Professor-plum/BSides-SLC-Badge-2020/resources/Chess_clean.jpg

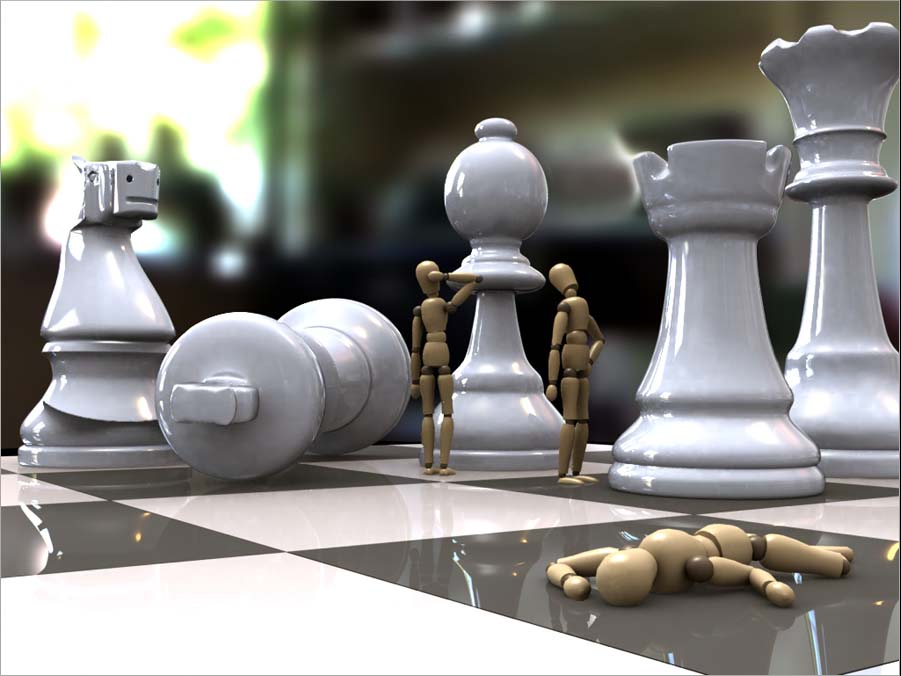
resources/Chess_clean.jpg
