Professor-plum/BSides-SLC-Badge-2020/source/BsidesSLC2020/Core/Inc/bsides_logo.h

/*
 * bsides_logo.h
 *
 *  Created on: Nov 3, 2019
 *      Author: plum
 */

#ifndef INC_BSIDES_LOGO_H_
#define INC_BSIDES_LOGO_H_

#define bsides_width 104
#define bsides_height 144
static const char bsides_bits[] = {
  0x00, 0x00, 0x00, 0x00, 0x00, 0x80, 0xFF, 0x01, 0x00, 0x00, 0x00, 0x00,
  0x00, 0x00, 0x00, 0x00, 0x00, 0x00, 0xFC, 0xFF, 0x3F, 0x00, 0x00, 0x00,
  0x00, 0x00, 0x00, 0x00, 0x00, 0x00, 0xC0, 0xFF, 0xFF, 0xFF, 0x03, 0x00,
  0x00, 0x00, 0x00, 0x00, 0x00, 0x00, 0x00, 0xF8, 0xFF, 0xFF, 0xFF, 0x1F,
  0x00, 0x00, 0x00, 0x00, 0x00, 0x00, 0x00, 0x00, 0xFF, 0xFF, 0xE7, 0xFF,
  0xFF, 0x00, 0x00, 0x00, 0x00, 0x00, 0x00, 0x00, 0xC0, 0xFF, 0x07, 0x00,
  0xE0, 0xFF, 0x03, 0x00, 0x00, 0x00, 0x00, 0x00, 0x00, 0xF0, 0x7F, 0x00,
  0x00, 0x00, 0xFE, 0x0F, 0x00, 0x00, 0x00, 0x00, 0x00, 0x00, 0xFC, 0x0F,
  0x00, 0x00, 0x00, 0xF0, 0x3F, 0x00, 0x00, 0x00, 0x00, 0x00, 0x00, 0xFE,
  0x03, 0x00, 0x00, 0x00, 0xC0, 0x7F, 0x00, 0x00, 0x00, 0x00, 0x00, 0x80,
  0xFF, 0x00, 0x00, 0x00, 0x00, 0x00, 0xFF, 0x01, 0x00, 0x00, 0x00, 0x00,
  0xC0, 0x3F, 0x00, 0x00, 0x00, 0x00, 0x00, 0xFC, 0x03, 0x00, 0x00, 0x00,
  0x00, 0xF0, 0x0F, 0x00, 0x00, 0x00, 0x00, 0x00, 0xF0, 0x0F, 0x00, 0x00,
  0x00, 0x00, 0xF8, 0x03, 0x00, 0x00, 0x00, 0x00, 0x00, 0xC0, 0x1F, 0x00,
  0x00, 0x00, 0x00, 0xFC, 0x01, 0x00, 0x00, 0x00, 0x00, 0x00, 0x80, 0x3F,
  0x00, 0x00, 0x00, 0x00, 0xFE, 0x00, 0x00, 0x00, 0x00, 0x00, 0x00, 0x00,
  0x7F, 0x00, 0x00, 0x00, 0x00, 0x3F, 0x00, 0x00, 0x00, 0x00, 0x00, 0x00,
  0x00, 0xFC, 0x00, 0x00, 0x00, 0x80, 0x1F, 0x00, 0x00, 0x00, 0x00, 0x00,
  0x00, 0x00, 0xF8, 0x01, 0x00, 0x00, 0xC0, 0x0F, 0x00, 0x00, 0x00, 0x00,
  0x00, 0x00, 0x00, 0xF0, 0x03, 0x00, 0x00, 0xE0, 0x07, 0x00, 0x00, 0x00,
  0x00, 0x00, 0x00, 0x00, 0xE0, 0x07, 0x00, 0x00, 0xF0, 0x03, 0x00, 0x00,
  0x00, 0x00, 0x03, 0x00, 0x00, 0xC0, 0x0F, 0x00, 0x00, 0xF0, 0x01, 0x00,
  0x00, 0x00, 0x80, 0x07, 0x00, 0x00, 0x80, 0x0F, 0x00, 0x00, 0xF8, 0x00,
  0x00, 0x00, 0x00, 0x80, 0x07, 0x00, 0x00, 0x00, 0x1F, 0x00, 0x00, 0x7C,
  0x00, 0x00, 0x00, 0x00, 0x80, 0x07, 0x00, 0x00, 0x00, 0x3E, 0x00, 0x00,
  0x7E, 0x00, 0x00, 0x00, 0x00, 0x80, 0x07, 0x00, 0x00, 0x00, 0x7E, 0x00,
  0x00, 0x3E, 0x00, 0x00, 0x00, 0x00, 0x80, 0x0F, 0x00, 0x00, 0x00, 0x7C,
  0x00, 0x00, 0x1F, 0x00, 0x00, 0x00, 0x00, 0x80, 0x0F, 0x00, 0x00, 0x00,
  0xF8, 0x00, 0x00, 0x1F, 0x00, 0x00, 0x00, 0x00, 0xC0, 0x0F, 0x00, 0x00,
  0x00, 0xF8, 0x00, 0x80, 0x0F, 0x00, 0x00, 0x00, 0x00, 0xC0, 0x1F, 0x00,
  0x00, 0x00, 0xF0, 0x01, 0x80, 0x0F, 0x00, 0x00, 0x00, 0x00, 0xC0, 0x1D,
  0x00, 0x00, 0x00, 0xF0, 0x01, 0xC0, 0x07, 0x00, 0x00, 0x00, 0x00, 0xC0,
  0x1D, 0x00, 0x00, 0x00, 0xE0, 0x03, 0xC0, 0x03, 0x00, 0x00, 0x00, 0x00,
  0xC0, 0x1D, 0x00, 0x00, 0x00, 0xC0, 0x03, 0xE0, 0x03, 0x00, 0x00, 0x00,
  0x00, 0xC0, 0x39, 0x00, 0x00, 0x00, 0xC0, 0x07, 0xE0, 0x01, 0x00, 0x00,
  0x00, 0x00, 0xE0, 0x39, 0x00, 0x00, 0x00, 0x80, 0x07, 0xF0, 0x01, 0x00,
  0x00, 0x00, 0x00, 0xE0, 0x38, 0x00, 0x00, 0x00, 0x80, 0x0F, 0xF0, 0x01,
  0x00, 0x00, 0x00, 0x00, 0xE0, 0x78, 0x00, 0x00, 0x00, 0x80, 0x0F, 0xF0,
  0x00, 0x00, 0x00, 0x00, 0x00, 0xE0, 0x70, 0x00, 0x00, 0x00, 0x00, 0x0F,
  0xF8, 0x00, 0x00, 0x00, 0x00, 0x00, 0xE0, 0x70, 0x00, 0x00, 0x00, 0x00,
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
  };


#endif /* INC_BSIDES_LOGO_H_ */
