Professor-plum/BSides-SLC-Badge-2020/source/BsidesSLC2020/Core/Inc/fakeDisk.h

#ifndef FAKE_DISK
#define FAKE_DISK

const uint8_t fake_mbr[] = {
		0xeb, 0x3c, 0x90,
		'P', 'l', 'u', 'm', ' ', 'F', 'S', 0,
		0x00, 0x02,
		0x04,
		0x01, 0x00,
		0x02,
		0x70, 0x00,
		0x00, 0x08, // 0x00, 0x08  Small Sectors 0x800 == 2048
		0xf8,
		0x02, 0x00, // 0x02, 0x00  Sector per FAT
		0x20, 0x00,
		0x40, 0x00,
		0x00, 0x00, 0x00, 0x00,
		0x00, 0x00, 0x00, 0x00,
		0x80,
		0x00,
		0x29,
		'P','L','U','M',
		'C', 'A', 'S', 'E', ' ', 'F', 'I', 'L', 'E', ' ', ' ',
		'F', 'A', 'T', '1', '2', ' ', ' ', ' '
};

const uint8_t fake_fat[] = {
		0xF8, 0xFF, 0xFF, 0x00, 0x40, 0x00, 0x05, 0x60, 0x00, 0x07, 0x80, 0x00, 0x09, 0xA0, 0x00, 0x0B,
		0xC0, 0x00, 0x0D, 0xE0, 0x00, 0x0F, 0x00, 0x01, 0x11, 0x20, 0x01, 0x13, 0x40, 0x01, 0xFF, 0x6F,
		0x01, 0x17, 0x80, 0x01, 0x19, 0xA0, 0x01, 0x1B, 0xC0, 0x01, 0x1D, 0xE0, 0x01, 0x1F, 0x00, 0x02,
		0x21, 0x20, 0x02, 0x23, 0x40, 0x02, 0xFF, 0x6F, 0x02, 0x27, 0x80, 0x02, 0x29, 0xA0, 0x02, 0x2B,
		0xC0, 0x02, 0x2D, 0xE0, 0x02, 0x2F, 0x00, 0x03, 0x31, 0x20, 0x03, 0x33, 0x40, 0x03, 0x35, 0x60,
		0x03, 0x37, 0x80, 0x03, 0x39, 0xA0, 0x03, 0x3B, 0xC0, 0x03, 0x3D, 0xE0, 0x03, 0x3F, 0x00, 0x04,
		0x41, 0xF0, 0xFF, 0x43, 0x40, 0x04, 0x45, 0x60, 0x04, 0x47, 0x80, 0x04, 0x49, 0xA0, 0x04, 0x4B,
		0xC0, 0x04, 0x4D, 0xE0, 0x04, 0x4F, 0x00, 0x05, 0x51, 0x20, 0x05, 0x53, 0xF0, 0xFF, 0x00, 0x00
};
//const uint8_t fake_fat[] = {0xf8, 0xff, 0xff, 0x00, 0xf0, 0xff, 0x05, 0x60, 0x00, 0x07, 0xf0, 0xff, 0xff, 0x0f};
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
