Professor-plum/BSides-SLC-Badge-2020/source/BsidesSLC2020/Core/Inc/custom_bus.h

/**
  ******************************************************************************
  * @file           : custom_bus.h
  * @brief          : header file for the BSP BUS IO driver
  ******************************************************************************
  * @attention
  *
  * <h2><center>&copy; Copyright (c) 2020 STMicroelectronics.
  * All rights reserved.</center></h2>
  *
  * This software component is licensed by ST under Ultimate Liberty license
  * SLA0044, the "License"; You may not use this file except in compliance with
  * the License. You may obtain a copy of the License at:
  *                             www.st.com/SLA0044
  *
  ******************************************************************************
*/

/* Define to prevent recursive inclusion -------------------------------------*/
#ifndef CUSTOM_BUS_H
#define CUSTOM_BUS_H

#ifdef __cplusplus
 extern "C" {
#endif

/* Includes ------------------------------------------------------------------*/
#include "custom_conf.h"
#include "custom_errno.h"

/** @addtogroup BSP
  * @{
  */

/** @addtogroup CUSTOM
  * @{
  */

/** @defgroup CUSTOM_BUS CUSTOM BUS
  * @{
  */

/** @defgroup CUSTOM_BUS_Exported_Constants CUSTOM BUS Exported Constants
  * @{
  */

#define BUS_I2C1_INSTANCE I2C1
#define BUS_I2C1_SCL_GPIO_PIN GPIO_PIN_6
#define BUS_I2C1_SCL_GPIO_AF GPIO_AF1_I2C1
#define BUS_I2C1_SCL_GPIO_CLK_ENABLE() __HAL_RCC_GPIOB_CLK_ENABLE()
#define BUS_I2C1_SCL_GPIO_PORT GPIOB
#define BUS_I2C1_SCL_GPIO_CLK_DISABLE() __HAL_RCC_GPIOB_CLK_DISABLE()
#define BUS_I2C1_SDA_GPIO_PIN GPIO_PIN_7
#define BUS_I2C1_SDA_GPIO_AF GPIO_AF1_I2C1
#define BUS_I2C1_SDA_GPIO_CLK_ENABLE() __HAL_RCC_GPIOB_CLK_ENABLE()
#define BUS_I2C1_SDA_GPIO_PORT GPIOB
#define BUS_I2C1_SDA_GPIO_CLK_DISABLE() __HAL_RCC_GPIOB_CLK_DISABLE()
#ifndef BUS_I2C1_POLL_TIMEOUT
   #define BUS_I2C1_POLL_TIMEOUT                0x1000U   
#endif
/* I2C1 Frequeny in Hz  */
#ifndef BUS_I2C1_FREQUENCY  
   #define BUS_I2C1_FREQUENCY  1000000U /* Frequency of I2Cn = 100 KHz*/
#endif

/**
  * @}
  */

/** @defgroup CUSTOM_BUS_Private_Types CUSTOM BUS Private types
  * @{
  */
#if (USE_HAL_I2C_REGISTER_CALLBACKS == 1)
typedef struct
{
  pI2C_CallbackTypeDef  pMspInitCb;
  pI2C_CallbackTypeDef  pMspDeInitCb;
}BSP_I2C_Cb_t;
#endif /* (USE_HAL_I2C_REGISTER_CALLBACKS == 1) */
/**
  * @}
  */
  
/** @defgroup CUSTOM_LOW_LEVEL_Exported_Variables LOW LEVEL Exported Constants
  * @{
  */

extern I2C_HandleTypeDef hi2c1;

/**
  * @}
  */

/** @addtogroup CUSTOM_BUS_Exported_Functions
  * @{
  */    

/* BUS IO driver over I2C Peripheral */
HAL_StatusTypeDef MX_I2C1_Init(I2C_HandleTypeDef* hi2c);
int32_t BSP_I2C1_Init(void);
int32_t BSP_I2C1_DeInit(void);
int32_t BSP_I2C1_IsReady(uint16_t DevAddr, uint32_t Trials);
int32_t BSP_I2C1_WriteReg(uint16_t Addr, uint16_t Reg, uint8_t *pData, uint16_t Length);
int32_t BSP_I2C1_ReadReg(uint16_t Addr, uint16_t Reg, uint8_t *pData, uint16_t Length);
int32_t BSP_I2C1_WriteReg16(uint16_t Addr, uint16_t Reg, uint8_t *pData, uint16_t Length);
int32_t BSP_I2C1_ReadReg16(uint16_t Addr, uint16_t Reg, uint8_t *pData, uint16_t Length);
int32_t BSP_I2C1_Send(uint16_t DevAddr, uint8_t *pData, uint16_t Length);
int32_t BSP_I2C1_Recv(uint16_t DevAddr, uint8_t *pData, uint16_t Length);
int32_t BSP_I2C1_SendRecv(uint16_t DevAddr, uint8_t *pTxdata, uint8_t *pRxdata, uint16_t Length);
#if (USE_HAL_I2C_REGISTER_CALLBACKS == 1)
int32_t BSP_I2C1_RegisterDefaultMspCallbacks (void);
int32_t BSP_I2C1_RegisterMspCallbacks (BSP_I2C_Cb_t *Callbacks);
#endif /* (USE_HAL_I2C_REGISTER_CALLBACKS == 1) */

int32_t BSP_GetTick(void);

/**
  * @}
  */

/**
  * @}
  */

/**
  * @}
  */

/**
  * @}
  */
#ifdef __cplusplus
}
#endif

#endif /* CUSTOM_BUS_H */

/************************ (C) COPYRIGHT STMicroelectronics *****END OF FILE****/
