Professor-plum/BSides-SLC-Badge-2020/source/BsidesSLC2020/Core/Inc/RTE_Components.h

/**
  ******************************************************************************
  * @file    
  * @author  MCD Application Team
  * @version V2.0.0
  ******************************************************************************
  * @attention
  *
  * COPYRIGHT(c) 2020 STMicroelectronics
  *
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
  */
  /* Define to prevent recursive inclusion -------------------------------------*/
#ifndef  __RTE_COMPONENTS_H__
#define  __RTE_COMPONENTS_H__ 

/* Defines ------------------------------------------------------------------*/
/* STMicroelectronics.X-CUBE-MEMS1.6.2.0 */
#define LIS2DH12_ACC_I2C
/* STMicroelectronics.X-CUBE-NFC4.1.4.0 */
#define LIB_NDEF
#define Interface
#define ST25DV_NFC4_I2C 
 
#endif /* __RTE_COMPONENTS_H__ */
