Professor-plum/BSides-SLC-Badge-2020/source/BsidesSLC2020/Core/Inc/bigdigits.h

#ifndef BIG_DIGITS_H
#define BIG_DIGITS_H

#define BD_WIDTH	14
#define BD_HEIGHT	21

static const char bigDigits[] = {
		  0x0F, 0xC0, 0x3F, 0xF0, 0x3F, 0xF0, 0x78, 0x78, 0x70, 0x38, 0xF0, 0x38,
		  0xE0, 0x1C, 0xE0, 0x1C, 0xE0, 0x1C, 0xE0, 0x1C, 0xE0, 0x1C, 0xE0, 0x1C,
		  0xE0, 0x1C, 0xE0, 0x1C, 0xE0, 0x1C, 0xF0, 0x3C, 0x70, 0x38, 0x78, 0x78,
		  0x3F, 0xF0, 0x3F, 0xF0, 0x0F, 0xC0, 0x00, 0x60, 0x00, 0xE0, 0x01, 0xE0,
		  0x03, 0xE0, 0x07, 0xE0, 0x0E, 0xE0, 0x0C, 0xE0, 0x08, 0xE0, 0x00, 0xE0,
		  0x00, 0xE0, 0x00, 0xE0, 0x00, 0xE0, 0x00, 0xE0, 0x00, 0xE0, 0x00, 0xE0,
		  0x00, 0xE0, 0x00, 0xE0, 0x00, 0xE0, 0x00, 0xE0, 0x00, 0xE0, 0x00, 0xE0,
		  0x0F, 0xC0, 0x3F, 0xE0, 0x7F, 0xF0, 0x70, 0xF8, 0xE0, 0x78, 0xE0, 0x38,
		  0x00, 0x38, 0x00, 0x38, 0x00, 0x70, 0x00, 0x70, 0x00, 0xE0, 0x01, 0xC0,
		  0x03, 0x80, 0x07, 0x00, 0x0E, 0x00, 0x1C, 0x00, 0x38, 0x00, 0x70, 0x00,
		  0xFF, 0xF8, 0xFF, 0xF8, 0xFF, 0xF8, 0x0F, 0x80, 0x3F, 0xE0, 0x7F, 0xF0,
		  0xF0, 0x78, 0xE0, 0x38, 0x00, 0x38, 0x00, 0x38, 0x00, 0x38, 0x00, 0xF0,
		  0x07, 0xE0, 0x07, 0xF0, 0x00, 0x38, 0x00, 0x3C, 0x00, 0x1C, 0x00, 0x1C,
		  0xE0, 0x1C, 0xF0, 0x3C, 0x70, 0x78, 0x7F, 0xF8, 0x3F, 0xF0, 0x0F, 0xC0,
		  0x00, 0x30, 0x00, 0x70, 0x00, 0xF0, 0x01, 0xF0, 0x01, 0xF0, 0x03, 0xF0,
		  0x07, 0x70, 0x0E, 0x70, 0x1E, 0x70, 0x1C, 0x70, 0x38, 0x70, 0x70, 0x70,
		  0xE0, 0x70, 0xFF, 0xFC, 0xFF, 0xFC, 0xFF, 0xFC, 0x00, 0x70, 0x00, 0x70,
		  0x00, 0x70, 0x00, 0x70, 0x00, 0x70, 0x3F, 0xF8, 0x3F, 0xF8, 0x3F, 0xF8,
		  0x70, 0x00, 0x70, 0x00, 0x70, 0x00, 0x70, 0x00, 0x77, 0xC0, 0xFF, 0xF0,
		  0xFF, 0xF8, 0xF0, 0x78, 0x00, 0x3C, 0x00, 0x1C, 0x00, 0x1C, 0x00, 0x1C,
		  0xE0, 0x1C, 0xE0, 0x38, 0x70, 0x78, 0x7F, 0xF0, 0x3F, 0xE0, 0x0F, 0xC0,
		  0x07, 0xE0, 0x1F, 0xF0, 0x3F, 0xF8, 0x38, 0x3C, 0x70, 0x1C, 0x70, 0x00,
		  0xE0, 0x00, 0xE3, 0xC0, 0xEF, 0xF0, 0xFF, 0xF8, 0xF8, 0x78, 0xF0, 0x3C,
		  0xE0, 0x1C, 0xE0, 0x1C, 0xE0, 0x1C, 0xE0, 0x1C, 0x70, 0x3C, 0x78, 0x78,
		  0x3F, 0xF8, 0x1F, 0xF0, 0x07, 0xC0, 0xFF, 0xF8, 0xFF, 0xF8, 0xFF, 0xF8,
		  0x00, 0x30, 0x00, 0x70, 0x00, 0xE0, 0x00, 0xC0, 0x01, 0xC0, 0x03, 0x80,
		  0x03, 0x80, 0x07, 0x00, 0x07, 0x00, 0x07, 0x00, 0x0E, 0x00, 0x0E, 0x00,
		  0x0E, 0x00, 0x0E, 0x00, 0x1C, 0x00, 0x1C, 0x00, 0x1C, 0x00, 0x1C, 0x00,
		  0x0F, 0xC0, 0x1F, 0xE0, 0x3F, 0xF0, 0x78, 0x78, 0x70, 0x38, 0x70, 0x38,
		  0x70, 0x38, 0x38, 0x70, 0x1F, 0xE0, 0x0F, 0xC0, 0x3F, 0xF0, 0x78, 0x78,
		  0x60, 0x3C, 0xE0, 0x1C, 0xE0, 0x1C, 0xE0, 0x1C, 0xF0, 0x3C, 0x78, 0x38,
		  0x7F, 0xF8, 0x3F, 0xF0, 0x0F, 0xC0, 0x0F, 0x80, 0x3F, 0xE0, 0x7F, 0xF0,
		  0x78, 0x78, 0xF0, 0x38, 0xE0, 0x1C, 0xE0, 0x1C, 0xE0, 0x1C, 0xE0, 0x1C,
		  0xF0, 0x3C, 0x78, 0x7C, 0x7F, 0xFC, 0x3F, 0xDC, 0x0F, 0x1C, 0x00, 0x1C,
		  0x00, 0x38, 0xE0, 0x38, 0xF0, 0x70, 0x7F, 0xF0, 0x3F, 0xE0, 0x1F, 0x80
};


#endif
