Professor-plum/BSides-SLC-Badge-2020/source/BsidesSLC2020/Core/Inc/images.h

#ifndef IMAGES_H
#define IMAGES_H

#define DIALOG_BASE     0x40000
#define IMAGES_BASE		(DIALOG_BASE+0x8000)
#define LOGO_IMG		(IMAGES_BASE+0x000)
#define	BOSS_IMG		(IMAGES_BASE+0x700)
#define	D_GUY_IMG		(IMAGES_BASE+0xB00)
#define	D_GIRL_IMG		(IMAGES_BASE+0xF00)
#define	ENEMY_IMG		(IMAGES_BASE+0x1300)
#define	GIRL_IMG		(IMAGES_BASE+0x1700)
#define	ITGUY_IMG		(IMAGES_BASE+0x1B00)
#define	WORKER_IMG		(IMAGES_BASE+0x1F00)
#define COMP_IMG		(IMAGES_BASE+0x2300)
#define ENG_IMG			(IMAGES_BASE+0x2700)

#define FRONT_ROOM  	(IMAGES_BASE+0x2F00)
#define COMP_ROOM   	(IMAGES_BASE+0x2B00)
#define REPAIR_ROOM 	(IMAGES_BASE+0x3300)
#define IT_ROOM     	(IMAGES_BASE+0x3700)
#define BREAK_ROOM  	(IMAGES_BASE+0x3B00)
#define MEET_ROOM   	(IMAGES_BASE+0x3F00)
#define BACK_ROOM   	(IMAGES_BASE+0x4300)
#define TUNNEL_ROOM 	(IMAGES_BASE+0x4700)
#define SUPPLY_ROOM 	(IMAGES_BASE+0x4B00)
#define SECRET_ROOM 	(IMAGES_BASE+0x4F00)
#define FRONT2_ROOM 	(IMAGES_BASE+0x5300)
#define CAGE_ROOM 		(IMAGES_BASE+0x5700)
#define FIRE_ROOM 		(IMAGES_BASE+0x5B00)
#define YARD2_ROOM		(IMAGES_BASE+0x5F00)
#define SUPPLY2_IMG		(IMAGES_BASE+0x6300)

#define VIRUS_IMG		(IMAGES_BASE+0x6700)
#define ENDING_IMG		(IMAGES_BASE+0x6B00)
#define POW_IMG			(IMAGES_BASE+0x6F00)

#endif
